JAHNAN00/ChunithmControllerFor24inchDisplayer/arduino code/config.h

#ifndef CONFIG_H
#define CONFIG_H

#define SEND1 (7)
#define SEND2 (6)
#define SEND3 (5)
#define SEND4 (16)
#define SEND5 (14)
#define SEND6 (15)

#define RECE1 (A3)
#define RECE2 (A2)
#define RECE3 (A1)
#define RECE4 (A0)
#define RECE5 (10)
#define RECE6 (9)

#define LEVELON (900)
#define LEVELOFF (950)
#define LIGHT (4)


#endif
